dnet/colorimage-bp-led8x8/test_remote.py

#!/usr/bin/env python

from StringIO import StringIO
import unittest
import remote


class TestRemote(unittest.TestCase):
    def setUp(self):
        self.remote = remote.Remote(serial_class=MockSerial)

    def test_init(self):
        self.assertEqual(
                self.get_serial_buf().getvalue(),
                ''.join(chr(i << 4) for i in xrange(2 * remote.ROWS)))
        for pixel in remote.PIXELS:
            self.assertFalse(self.remote.get_pixel(pixel))

    def test_first_block(self):
        sb = self.get_serial_buf()
        sb.truncate(0)
        self.remote.set_pixel((0, 0), True)
        self.remote.flush_pixels()
        self.assertEqual(sb.getvalue(), '\x08')

    def test_second_block(self):
        sb = self.get_serial_buf()
        sb.truncate(0)
        self.remote.set_pixel((4, 0), True)
        self.remote.flush_pixels()
        self.assertEqual(sb.getvalue(), '\x18')
        sb.truncate(0)
        self.remote.set_pixel((5, 0), True)
        self.remote.flush_pixels()
        self.assertEqual(sb.getvalue(), '\x1c')

    def test_empty_flush(self):
        sb = self.get_serial_buf()
        sb.truncate(0)
        self.remote.flush_pixels()
        self.assertEquals(sb.getvalue(), '')

    def test_no_change_flush(self):
        sb = self.get_serial_buf()
        sb.truncate(0)
        self.remote.set_pixel((0, 0), False)
        self.remote.flush_pixels()
        self.assertEquals(sb.getvalue(), '')

    def test_full(self):
        sb = self.get_serial_buf()
        sb.truncate(0)
        for pixel in remote.PIXELS:
            self.remote.set_pixel(pixel, True)
        for pixel in remote.PIXELS:
            self.assertTrue(self.remote.get_pixel(pixel))
        self.remote.flush_pixels()
        self.assertEqual(
                sb.getvalue(),
                ''.join(chr((i << 4) | 0x0F) for i in xrange(2 * remote.ROWS)))

    def get_serial_buf(self):
        return self.remote.port.dut2tc


class MockSerial(object):
    def __init__(self, port, speed, timeout):
        self.dut2tc = StringIO()
        self.tried_read = False

    def write(self, data):
        pp = self.dut2tc.tell()
        self.dut2tc.write(data)
        self.dut2tc.seek(pp)

    def read(self):
        if self.tried_read:
            self.tried_read = False
            return 'B'
        else:
            self.tried_read = True
            return ''


if __name__ == '__main__':
    unittest.main()
